JarneMeylemans/PE2-JarneMeylemans-Lasergun/Documenten/kosten analyse.pdf

Component | Aantal gebruikt Aantal besteld | | Kost - aantal gebruikt | Kost - aantal besteld
32,768kHz crystal | 2 | 4 | 1,015 | 2,03
8 MHz crystal | 2 | 10 | 0,066 | 0,33
AMS 1117-3,3 | 2 | 50 | 0,0184 | 0,46
Bipolaire Transistor | 6 | 20 | 0,888 | 2,96
Bluepill STM32F103 board | 0 | 1 | 0 | 1,31
ESP8266 | 2 | 5 | 0,348 | 0,87
FlatBack Bolle lens 25mm | 1 | 10 | 0,19 | 1,9
FT232RL | 2 | 3 | 7,62 | 11,43
Header Jumper | 6 | 100 | 0,015 | 0,25
IR Emitter | 2 | 10 | 0,06 | 0,3
IR Transmitter | 2 | 10 | 0,06 | 0,3
JST connector kit | 1 | 1 | 0,71 | 0,71
micro switch roller | 2 | 10 | 0,332 | 1,66
Mini DC-DC step down buck converter | 2 | 4 | 0,235 | 0,47
Mini USB female socket | 2 | 20 | 0,076 | 0,76
OLED 128x64 | 2 | 4 | 0,755 | 1,51
Pin header set | 1 | 1 | 0,55 | 0,55
Pin header wire kit | 1 | 1 | 2 | 2
rotary encoder | 2 | 5 | 0,72 | 1,8
Screw blokaansluiting | 2 | 20 | 0,039 | 0,39
SMD condensatoren kit (0805) | 1 | 1 | 3,12 | 3,12
SMD LED groen (0805) | 1 | 100 | 0,0023 | 0,23
SMD LED rood (0805) | 1 | 100 | 0,0016 | 0,16
SMD weerstanden kit (0805) | 1 | 1 | 4,03 | 4,03
SMD weerstanden kit (1210) | 1 | 1 | 2,81 | 2,81
ST Link usb | 1 | 1 | 1,3 | 1,3
STM32F410RBT7TR | 2 | 5 | 7,34 | 18,35
switch key | 2 | 50 | 0,03 | 0,75
Ontwikkelen PCB | 1 | 1 | 23,39 | 23,39
Totale verzendkosten Aliexpress | | | 36,08 | 36,08
Totale verzendkosten Mouser | | | 10,55 | 10,55
