JarneMeylemans/PE2-JarneMeylemans-Lasergun/Documenten/pe2fin.pdf

Practice Enterprise final | 16-mei-2021 http://

Project beheerder
Project start/einde data | 16-feb-2021 - 25-mei-2021
% Gereed | 0%
Taak | 22
Personen | 0

Naam | Be gin dat um

Ein
d
dat
um
componenten kiezen | 16- 02-
| 21

02-
03-
21
datasheets componenten lezen | 16- 02-
| 21

02-
03-
21
Schakeling tekenen (KICAD) | 16- 02-
| 21

12-
03-
21
PCB layout tekenen | 15- 03-
| 21

30-
03-
21
PCB afgemaakt en besteld | 31- 03-
| 21

31-
03-
21
Test Code schrijven | 16- 02-
| 21

12-
04-
21
PCB SMD Componenten besteld | 23- 03-
| 21

23-
03-
21
PCB bestukken | 08- 04-
| 21

15-
04-
21
Eerste PCB bestukt | 16- 04-
| 21

16-
04-
21
Test Code overzetten naar nieuwe PCB | 19- 04-
| 21

27-
04-
21
Practice Enterprise final | 16-mei-2021
Taak | 2

Naam | Be gin dat um

Ein
d
dat
um
Code voor eigen bordje schrijven | 19- 04-
| 21

14-
05-
21
WIFI communicatie sotfware | 10- 05-
| 21

14-
05-
21
OLED code | 26- 04-
| 21

30-
04-
21
Rotary encoder code | 26- 04-
| 21

30-
04-
21
interface code schrijven | 03- 05-
| 21

07-
05-
21
IR communcatie code | 19- 04-
| 21

23-
04-
21
alle code bij elkaar plakkenb | 10- 05-
| 21

14-
05-
21
Ontwerpen van behuizing | 19- 04-
| 21

19-
04-
21
Printen van behuizing | 20- 04-
| 21

27-
04-
21
2de bordje bestukken | 09- 04-
| 21

15-
04-
21
Taak | 3

Naam | Be gin dat um

Ein
d
dat
um
behuizing klaar | 28- 04-
| 21

28-
04-
21
documentatie inorde brengen | 29- 04-
| 21

24-
05-
21
Taak | 4

## Gantt Grafiek

5

Naam | ......
componenten kiezen | ......
datasheets componenten lezen | ......
Schakeling tekenen (KICAD) | ......
PCB layout tekenen | ......
PCB afgemaakt en besteld | ......
Test Code schrijven | ......
PCB SMD Componenten besteld | ......
PCB bestukken | ......
Eerste PCB bestukt | ......
Test Code overzetten naar nieuwe PCB ......
Code voor eigen bordje schrijven | ......
WIFI communicatie sotfware | ......
OLED code | ......
Rotary encoder code | ......
interface code schrijven | ......
IR communcatie code | ......
alle code bij elkaar plakkenb | ......
Ontwerpen van behuizing | ......
Printen van behuizing | ......
2de bordje bestukken | ......
behuizing klaar | ......
documentatie inorde brengen | ......
Week 6 | Week 7 | Week 8 | Week 9 | Week 10 | Week 11 | Week 12 | Week 13 | Week 14 | Week 15 | Week 16 | Week 17 | Week 18 | Week 19 | Week 20 | Week 21 | Week 22 | Week 23 | Week 24 | Week 25 | Week 26
08-02-21 | 15-02-21 | 22-02-21 | 01-03-21 | 08-03-21 | 15-03-21 | 22-03-21 | 29-03-21 | 05-04-21 | 12-04-21 | 19-04-21 | 26-04-21 | 03-05-21 | 10-05-21 | 17-05-21 | 24-05-21 | 31-05-21 | 07-06-21 | 14-06-21 | 21-06-21 | 28-06-21
Schakeling tekenen (KICAD) datasheets componenten lezen componenten kiezen Test Code schrijven | PCB layout tekenen PCB SMD Componenten besteld PCB afgemaakt en besteld PCB bestukkenEerste PCB bestukt Test Code overzetten naar nieuwe PCB Printen van behuizing OLED code behuizing klaar | WIFI communicatie sotfware

## Personen-grafiek

6

Naam | Standaa...
Week 6 | Week 7 | Week 8 | Week 9 | Week 10 | Week 11 | Week 12 | Week 13 | Week 14 | Week 15 | Week 16 | Week 17 | Week 18 | Week 19 | Week 20 | Week 21 | Week 22 | Week 23 | Week 24 | Week 25 | Week 26
08-02-21 | 15-02-21 | 22-02-21 | 01-03-21 | 08-03-21 | 15-03-21 | 22-03-21 | 29-03-21 | 05-04-21 | 12-04-21 | 19-04-21 | 26-04-21 | 03-05-21 | 10-05-21 | 17-05-21 | 24-05-21 | 31-05-21 | 07-06-21 | 14-06-21 | 21-06-21 | 28-06-21

PCB SMD Componenten besteld PCB afgemaakt en besteld Eerste PCB bestukt behuizing klaar
