JarneMeylemans/PE2-JarneMeylemans-Lasergun/Documenten/Foto's/pcb-3dviewer.PNG

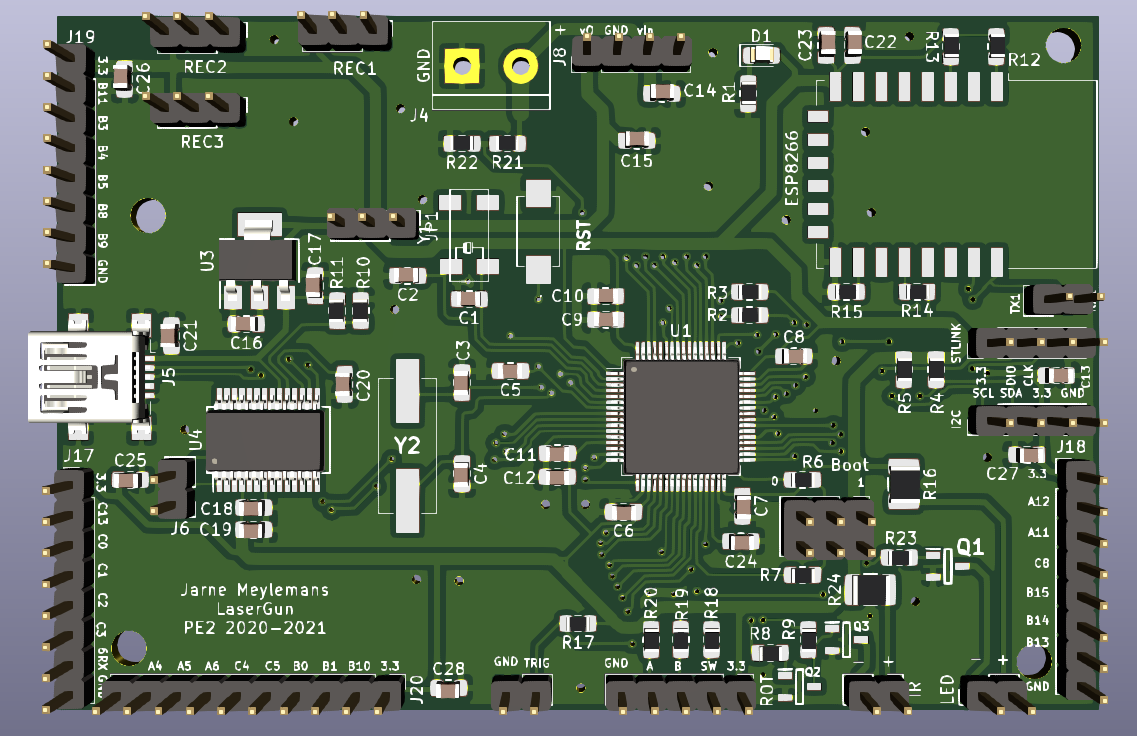
Documenten/Foto's/pcb-3dviewer.PNG
