JarneMeylemans/PE2-JarneMeylemans-Lasergun/Documenten/Foto's/UartOverIR.PNG

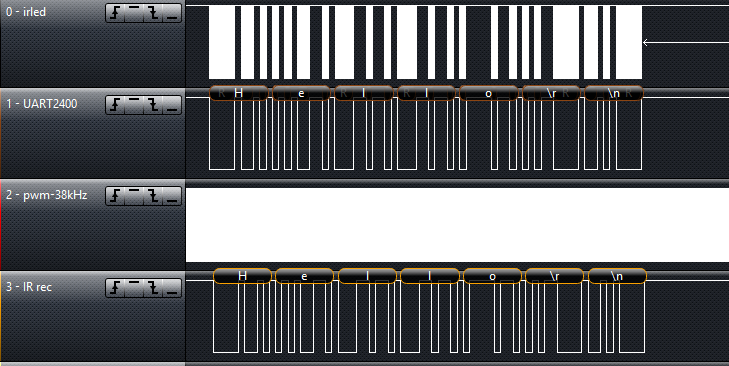
Documenten/Foto's/UartOverIR.PNG
