JarneMeylemans/PE2-JarneMeylemans-Lasergun/Documenten/Handleiding/Dia1.PNG

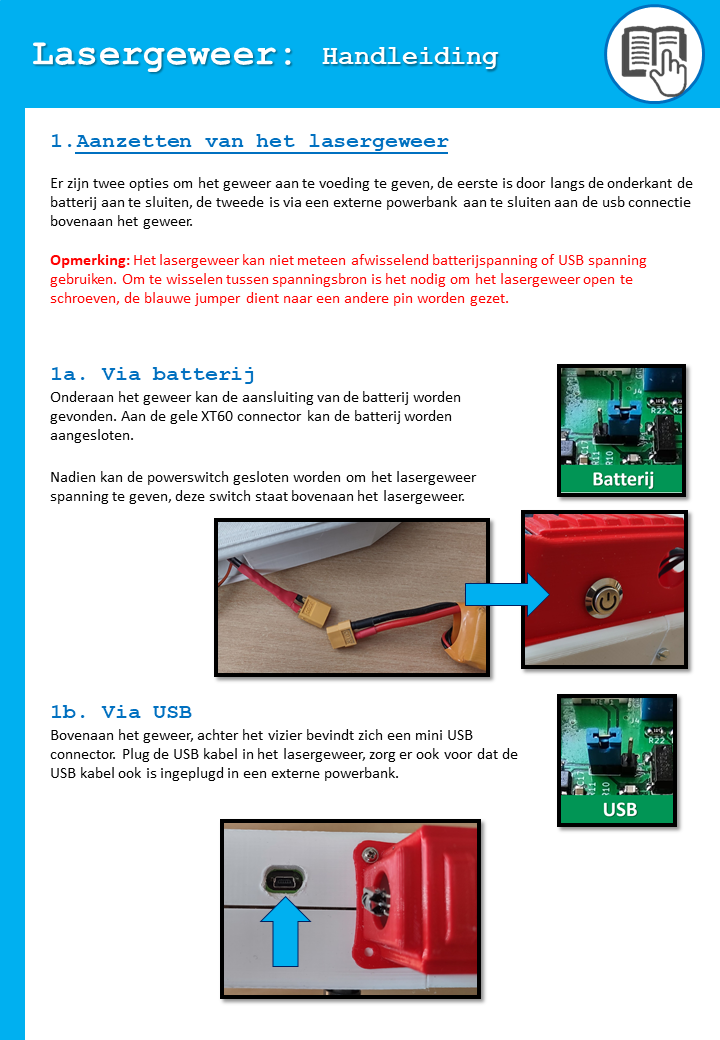
Documenten/Handleiding/Dia1.PNG
