JarneMeylemans/PE2-JarneMeylemans-Lasergun/Documenten/pe2.png

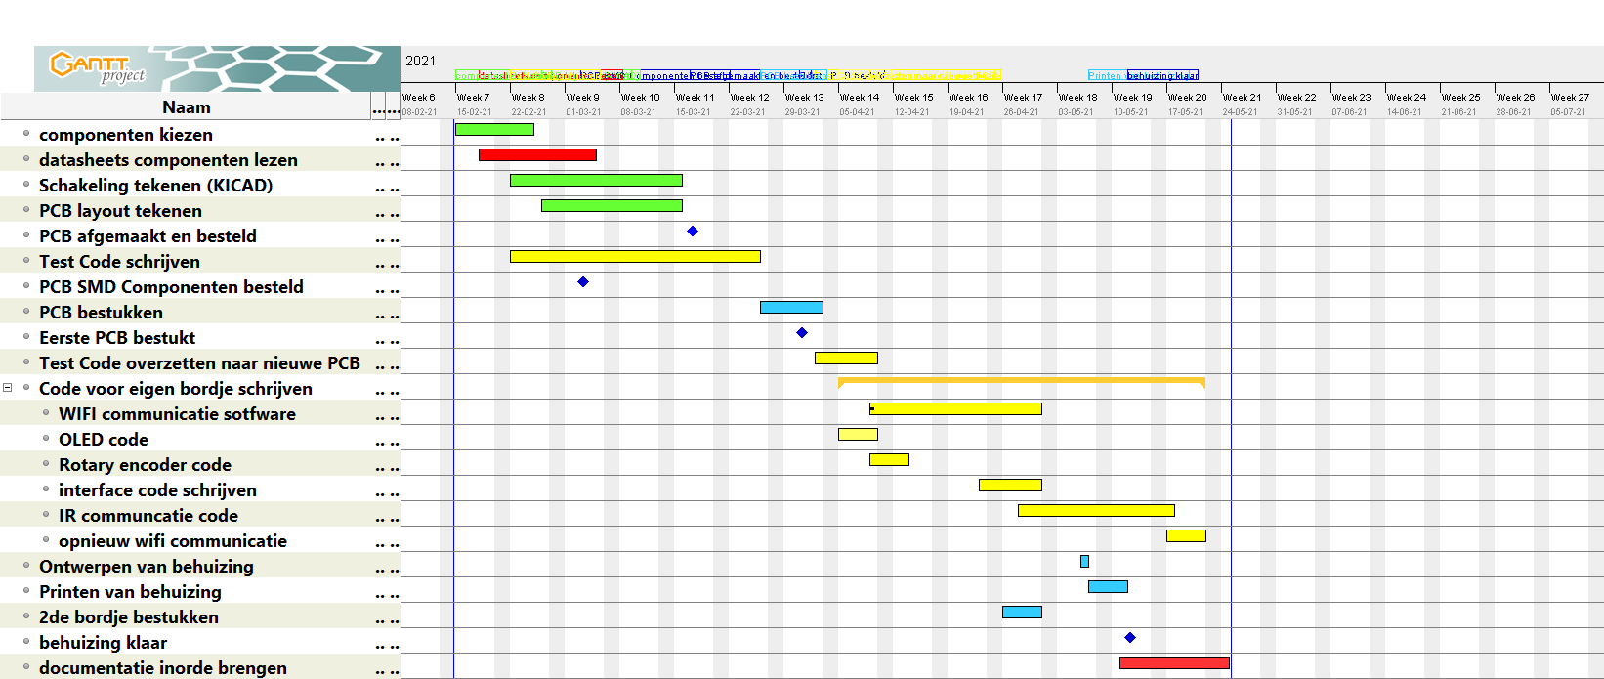
Documenten/pe2.png
