JarneMeylemans/PE2-JarneMeylemans-Lasergun/Documenten/SoftwareBlokschema's.pdf

# Main

# State Machine

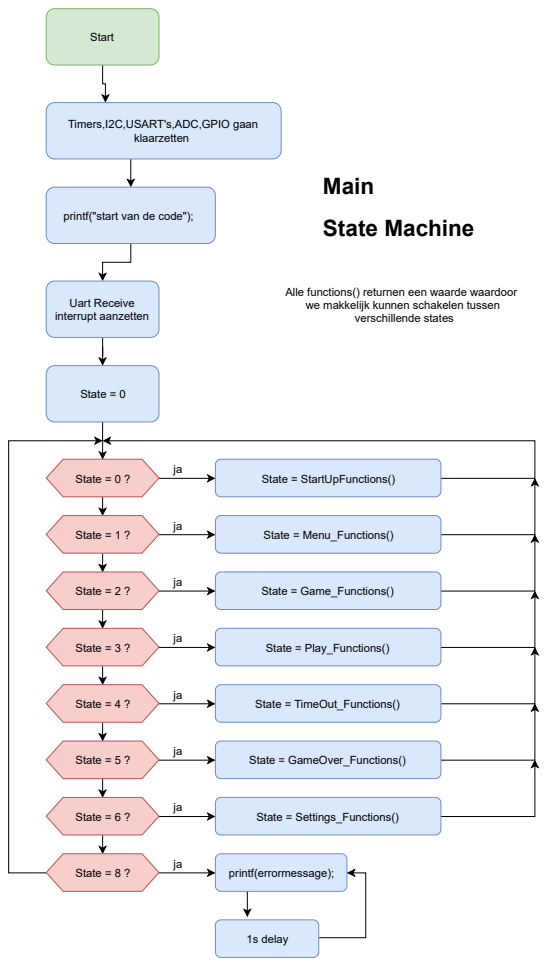
[picture p39: page 1]
Start; klaarzetten; State = 0; State = 0 ?; State = 1 ?; State = 2 ?; State = 3 ?; State = 4 ?; State = 5 ?; State = 6 ?; State = 8 ?; State = StartUpFunctions(); State = Menu_Functions(); State = Game_Functions(); State = Play_Functions(); State = TimeOut_Functions(); State = GameOver_Functions(); State = Settings_Functions(); printf(errormessage);; 1s delay; verschillende states; Uart Receive interrupt aanzetten

Timers,I2C,USART's,ADC,GPIO gaan

printf("start van de code");

Alle functions() returnen een waarde waardoor
we makkelijk kunnen schakelen tussen

# StartUp

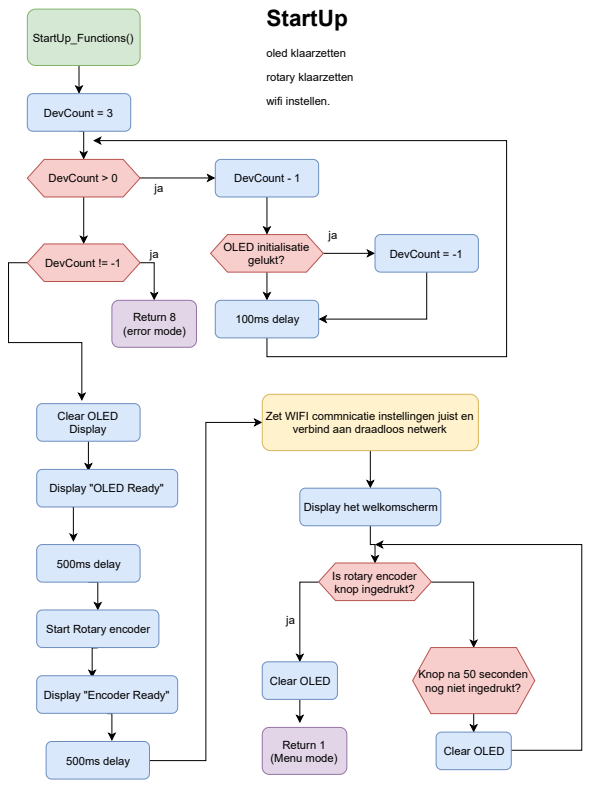
[picture p40: page 2]
StartUp_Functions(); DevCount = 3; DevCount > 0; DevCount - 1; OLED initialisatie; gelukt?; DevCount = -1; 100ms delay; DevCount != -1; Return 8 (error mode); Clear OLED Display; 500ms delay; Return 1; (Menu mode); Clear OLED; oled klaarzetten; rotary klaarzetten; wifi instellen.

Zet WIFI commnicatie instellingen juist en
verbind aan draadloos netwerk

Display "OLED Ready"

Display het welkomscherm

Is rotary encoder
knop ingedrukt?

Start Rotary encoder

nog niet ingedrukt? Clear OLED

Knop na 50 seconden

Display "Encoder Ready"

# Menu tonen

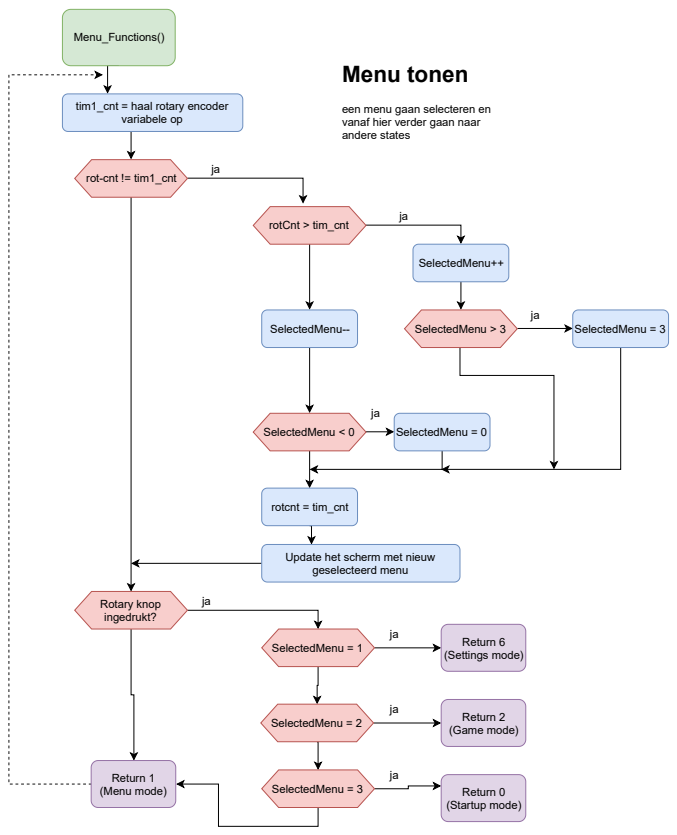
[picture p41: page 3]
Menu_Functions(); variabele op; rot-cnt != tim1_cnt; rotCnt > tim_cnt; SelectedMenu++; SelectedMenu--; SelectedMenu > 3; SelectedMenu = 3; SelectedMenu < 0; SelectedMenu = 0; rotcnt = tim_cnt; Rotary knop ingedrukt?; SelectedMenu = 1; SelectedMenu = 2; Return 1 (Menu mode); Return 6 (Settings mode); Return 2 (Game mode); Return 0 (Startup mode)

tim1_cnt = haal rotary encoder

een menu gaan selecteren en
vanaf hier verder gaan naar
andere states

Update het scherm met nieuw
geselecteerd menu

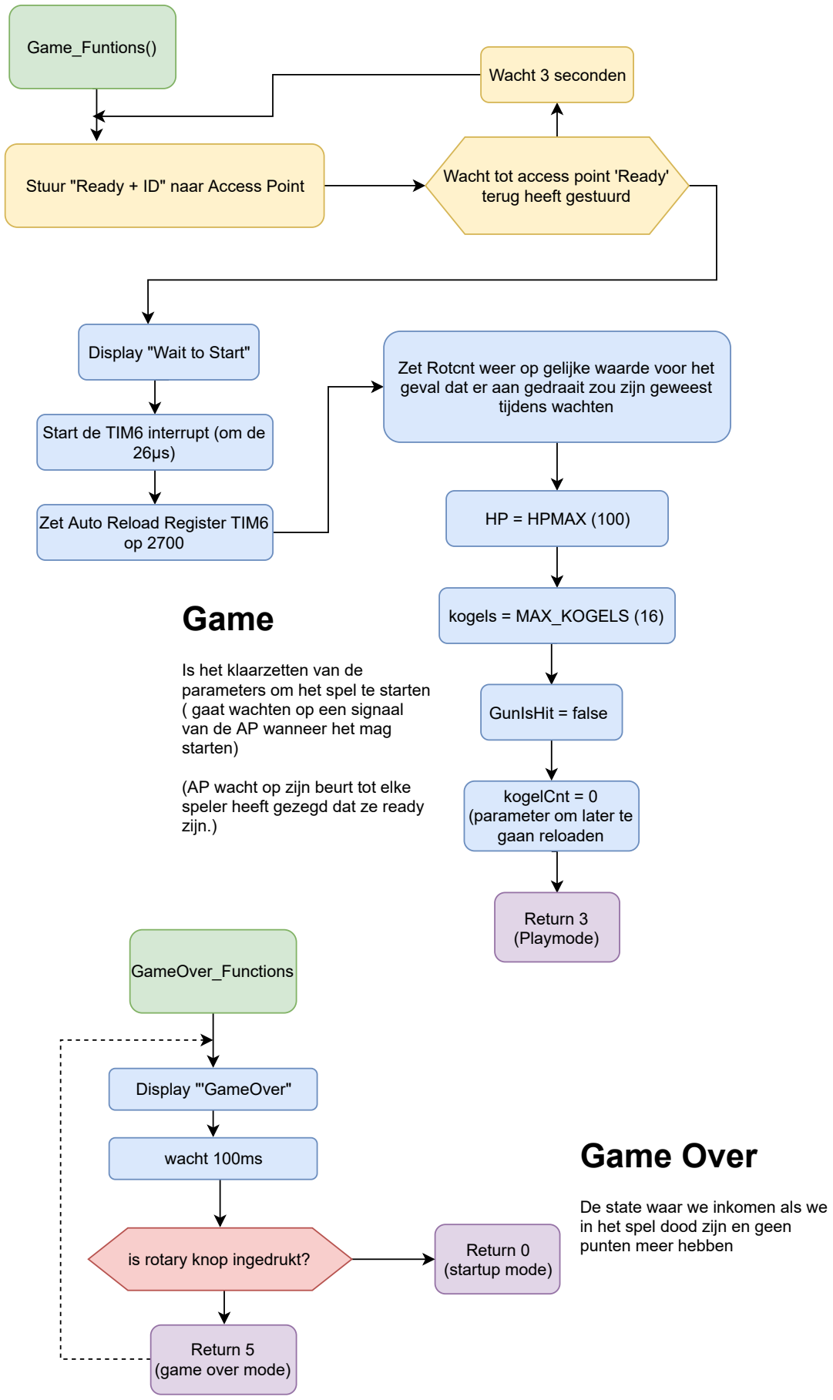
[picture p42: figure]
Game_Funtions(); terug heeft gestuurd; Wacht 3 seconden; Display "Wait to Start"; Start de TIM6 interrupt (om de 26µs); Zet Auto Reload Register TIM6 op 2700; tijdens wachten; HP = HPMAX (100); kogels = MAX_KOGELS (16); GunIsHit = false; kogelCnt = 0 (parameter om later te gaan reloaden; Return 3 (Playmode); Game; Is het klaarzetten van de parameters om het spel te starten ( gaat wachten op een signaal van de AP wanneer het mag starten); (AP wacht op zijn beurt tot elke speler heeft gezegd dat ze ready zijn.); GameOver_Functions; Display "'GameOver"; wacht 100ms; Return 0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

Stuur "Ready + ID" naar Access Point | Wacht tot access point 'Ready'

Zet Rotcnt weer op gelijke waarde voor het geval dat er aan gedraait zou zijn geweest

(startup mode) is rotary knop ingedrukt?

# Play the game

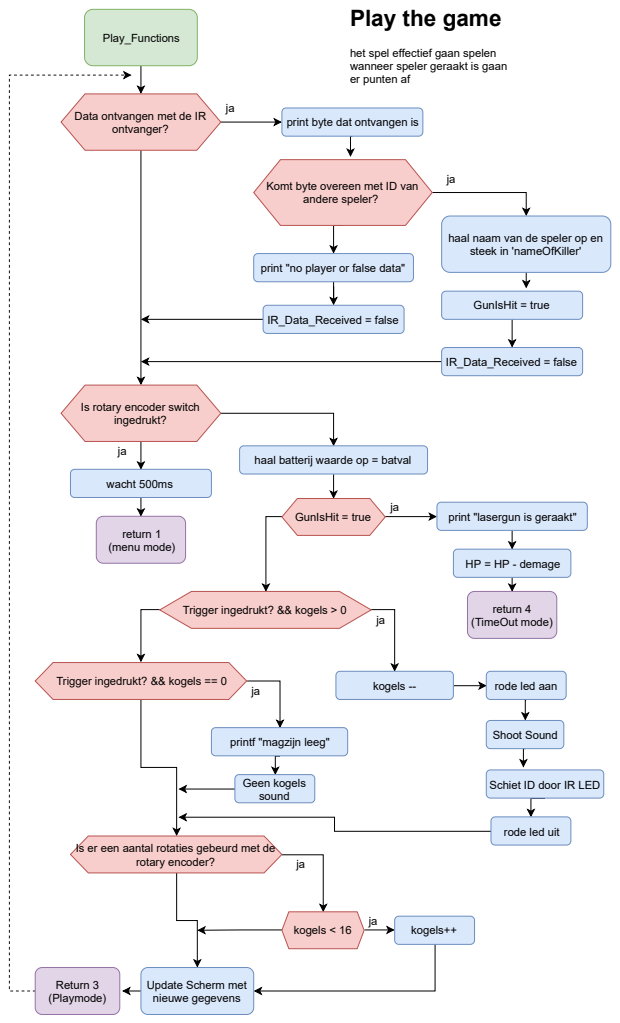
[picture p43: page 5]
Play_Functions; ontvanger?; print byte dat ontvangen is; IR_Data_Received = false; GunIsHit = true; wacht 500ms; return 1 (menu mode); print "lasergun is geraakt"; return 4 (TimeOut mode); Trigger ingedrukt? && kogels == 0; kogels --; rode led aan; Shoot Sound; Geen kogels sound; rotary encoder?; kogels < 16; kogels++; Return 3 (Playmode)

het spel effectief gaan spelen
wanneer speler geraakt is gaan
er punten af

Data ontvangen met de IR

Komt byte overeen met ID van
andere speler?

haal naam van de speler op en
steek in 'nameOfKiller'

print "no player or false data"

Is rotary encoder switch
ingedrukt?

haal batterij waarde op = batval

HP = HP - demage

Trigger ingedrukt? && kogels > 0

printf "magzijn leeg"

Schiet ID door IR LED

rode led uit

Is er een aantal rotaties gebeurd met de

Update Scherm met
nieuwe gegevens

# Time Out

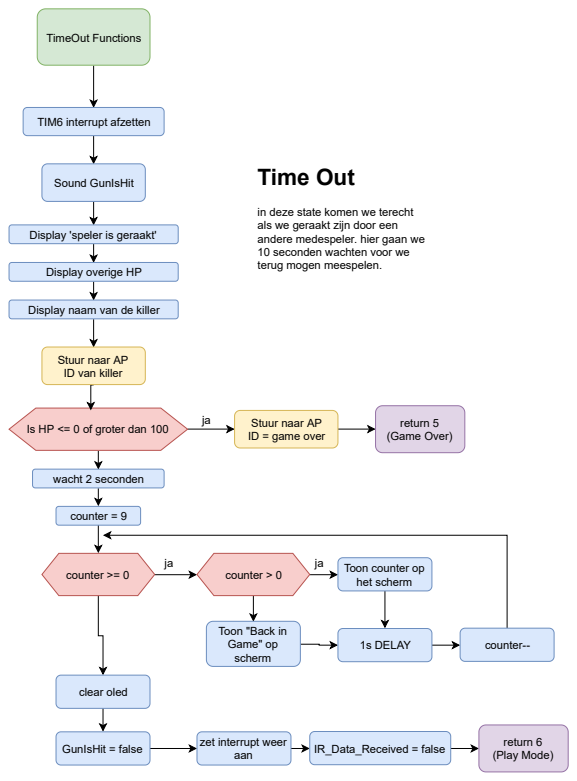
[picture p44: page 6]
TimeOut Functions; TIM6 interrupt afzetten; Sound GunIsHit; return 5 (Game Over); wacht 2 seconden; counter = 9; counter >= 0; counter > 0; Toon counter op; het scherm; 1s DELAY; counter--; clear oled; GunIsHit = false; zet interrupt weer; aan; IR_Data_Received = false; return 6; (Play Mode)

in deze state komen we terecht
als we geraakt zijn door een
andere medespeler. hier gaan we
10 seconden wachten voor we
terug mogen meespelen.

Display 'speler is geraakt'

Display overige HP

Display naam van de killer

Stuur naar AP
ID van killer

ID = game over

Is HP <= 0 of groter dan 100

Toon "Back in
Game" op
scherm

# Settings menu

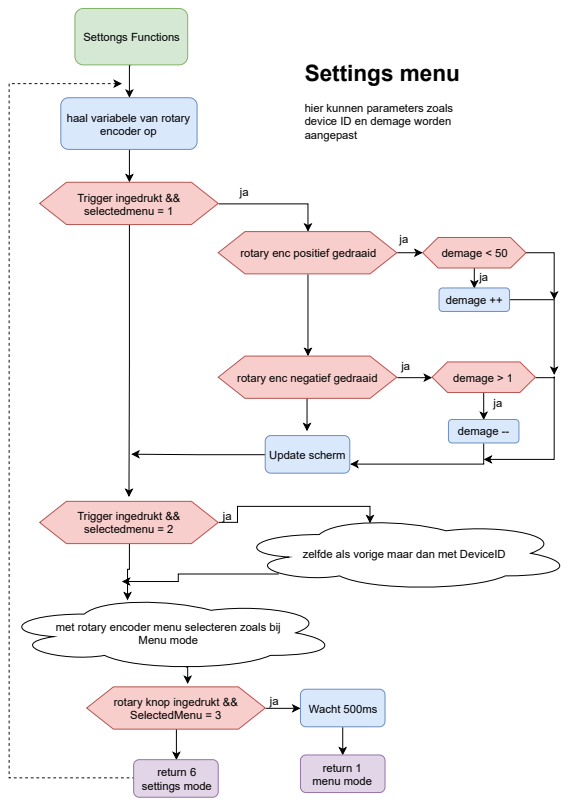
[picture p45: page 7]
Settongs Functions; Trigger ingedrukt && selectedmenu = 1; demage < 50; demage ++; demage > 1; demage --; Update scherm; Trigger ingedrukt && selectedmenu = 2; Menu mode; SelectedMenu = 3; Wacht 500ms; return 1 menu mode; return 6 settings mode

hier kunnen parameters zoals
device ID en demage worden
aangepast

haal variabele van rotary
encoder op

rotary enc positief gedraaid

rotary enc negatief gedraaid

zelfde als vorige maar dan met DeviceID

met rotary encoder menu selecteren zoals bij

rotary knop ingedrukt &&

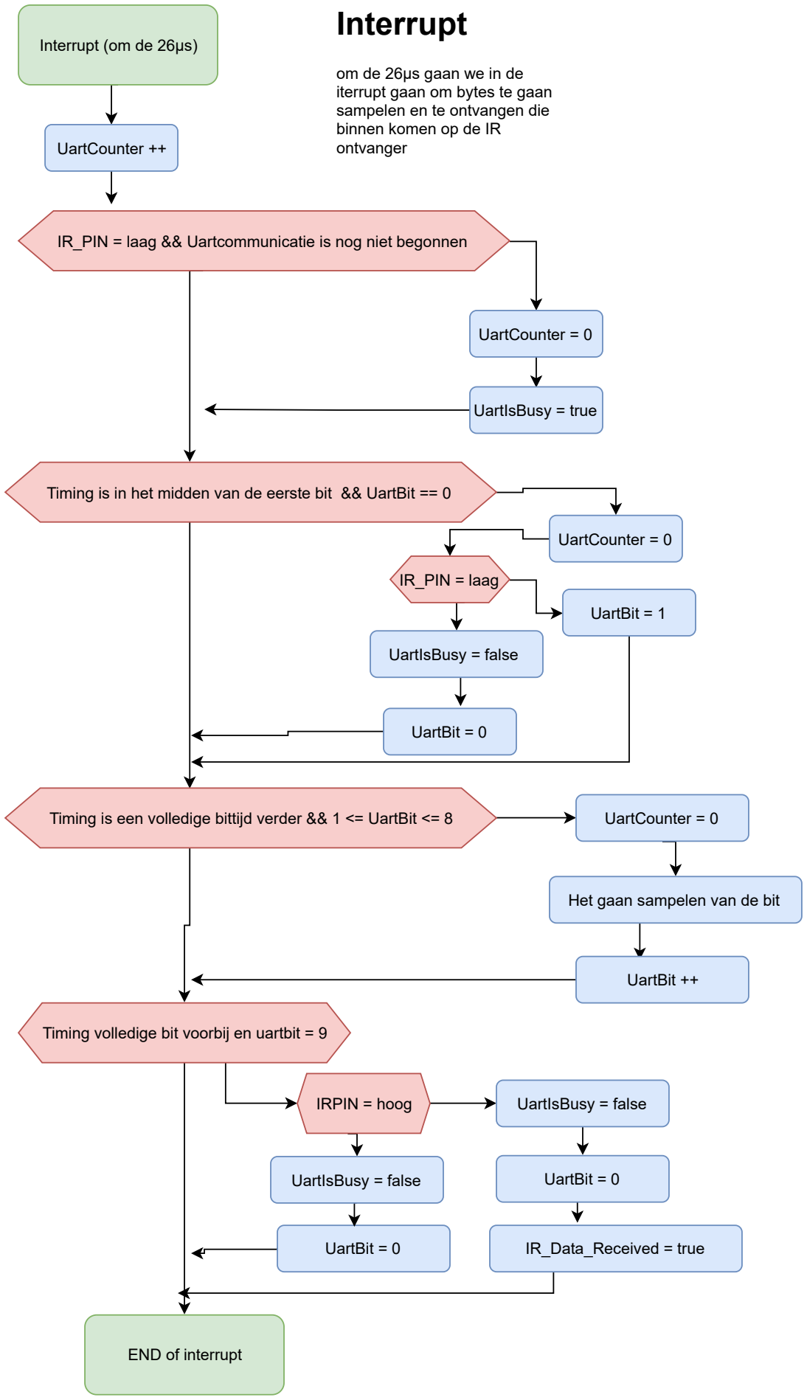
[picture p46: figure]
Interrupt (om de 26µs); UartCounter ++; UartCounter = 0; UartIsBusy = true; IR_PIN = laag; UartBit = 1; UartIsBusy = false; UartBit = 0; Het gaan sampelen van de bit; UartBit ++; IRPIN = hoog; IR_Data_Received = true; END of interrupt; Interrupt; om de 26µs gaan we in de iterrupt gaan om bytes te gaan sampelen en te ontvangen die binnen komen op de IR ontvanger

IR_PIN = laag && Uartcommunicatie is nog niet begonnen

Timing is in het midden van de eerste bit && UartBit == 0

Timing is een volledige bittijd verder && 1 <= UartBit <= 8 | UartCounter = 0

Timing volledige bit voorbij en uartbit = 9
