JarneMeylemans/PE2-JarneMeylemans-Lasergun/Project_Code/STM32F4/PE_LASERGUN_CODE_2apr/Core/Inc/Tones.h

#include "main.h"
#include "stm32f4xx_hal.h"


void Tone_Tim9( uint16_t frequency, uint8_t prescaler);
void Tone_GunShot(void);
void Tone_BulletsEmpty(void);
void Tone_GunIsHit(void);
void Tone_GameOver(void);
