JarneMeylemans/PE2-JarneMeylemans-Lasergun/Test_Code/ESP_AT_COMMANDS/Core/Inc/ESP8266_Functions.h

/*	ESP8266 FUNCTIES
 *
 * ESP8266_Functions.h
 * Created on: 15 feb 2021
 * Author: Jarne Meylemans
 *
 */

void ESP8266_Init(char *SSID, char *PASSWORD);

void ESP_Send_Uart(char *data);

void PC_Send_Uart(char *data);
